antmicro/jetson-orin-baseboard/assets/wireframe/wireframe_dimensions.png

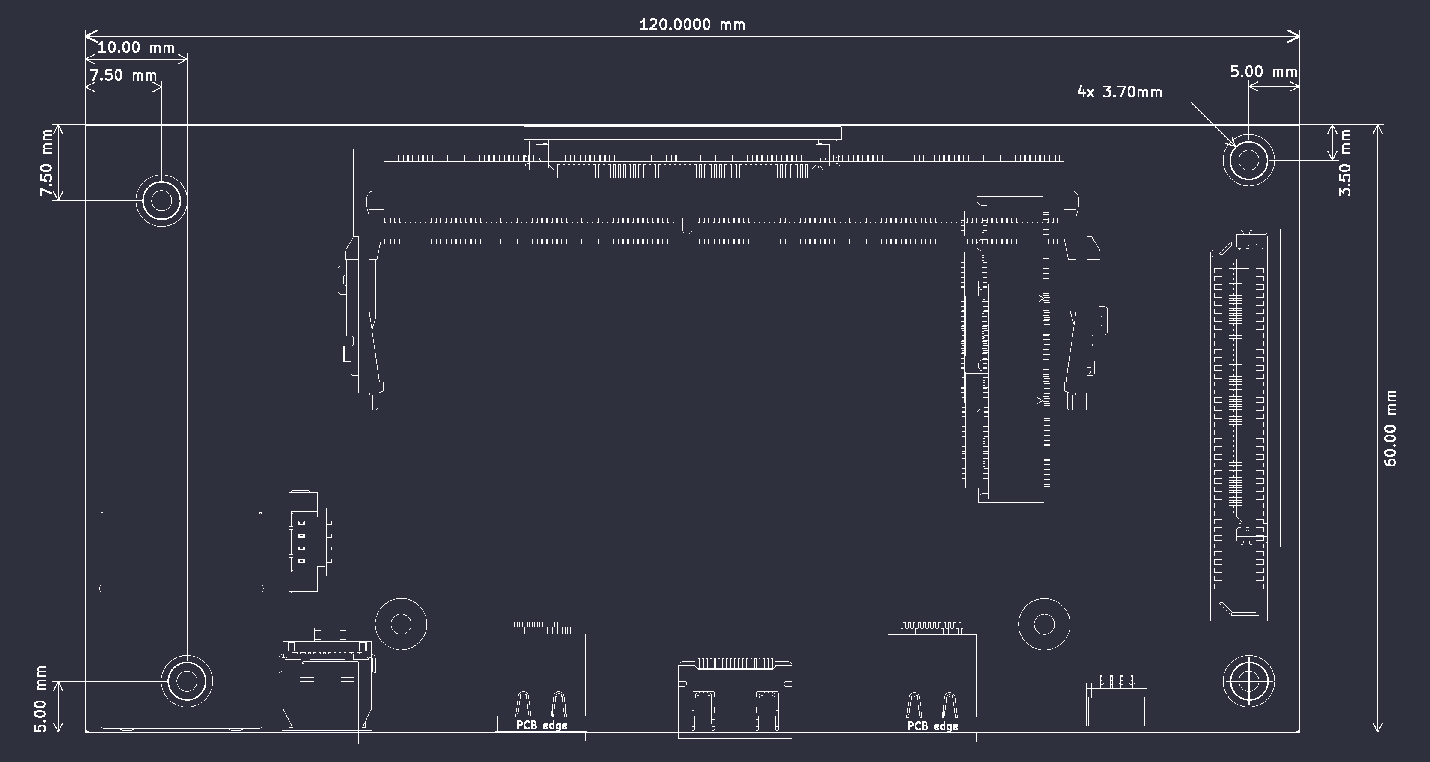
assets/wireframe/wireframe_dimensions.png
