antmicro/jetson-orin-baseboard/assets/wireframe/wireframe_dimensions_bottom.png

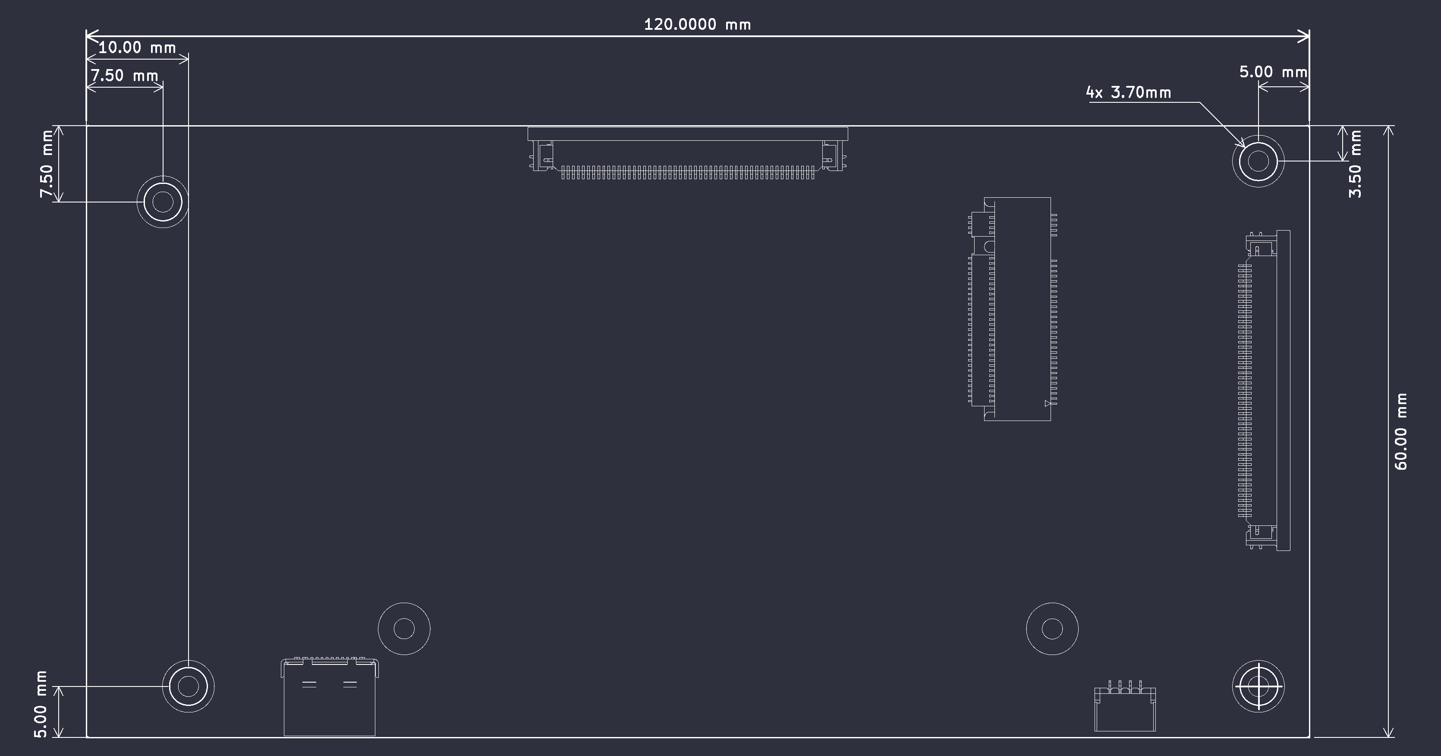
assets/wireframe/wireframe_dimensions_bottom.png
