antmicro/jetson-orin-baseboard/assets/wireframe/wireframe_dimensions_top.png

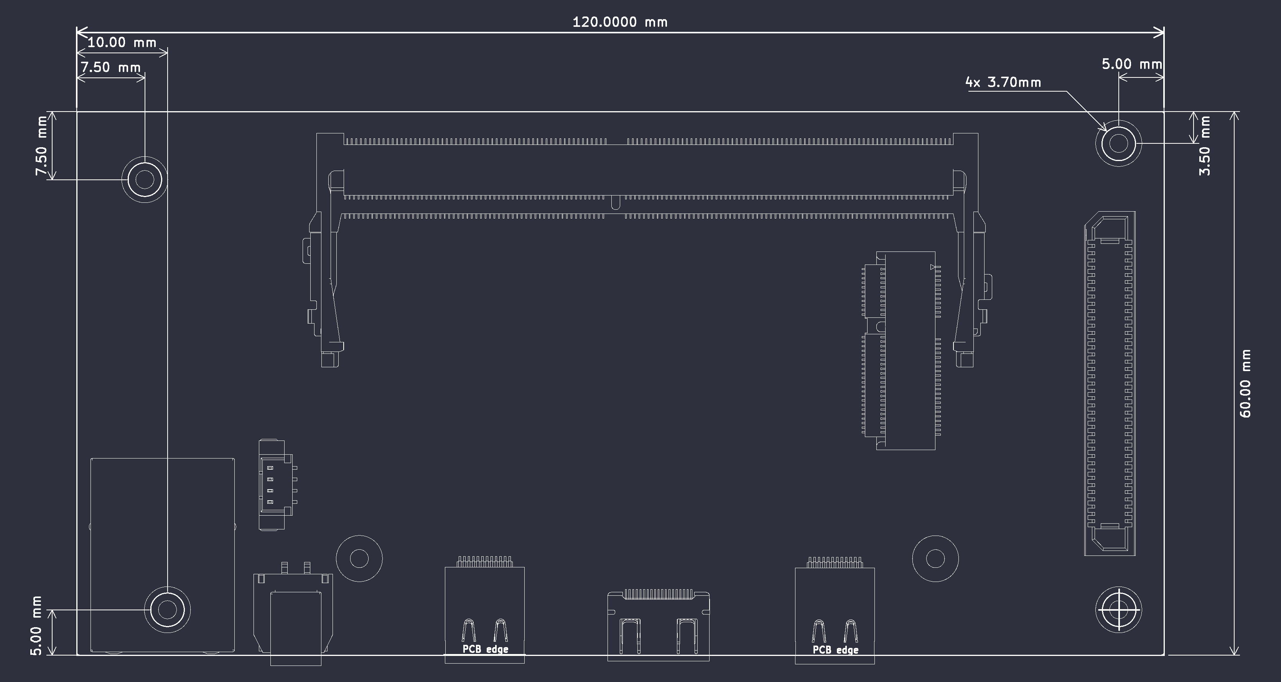
assets/wireframe/wireframe_dimensions_top.png
