antmicro/jetson-orin-baseboard/doc/source/img/3V3_eff_temp_vs_output_curr.png

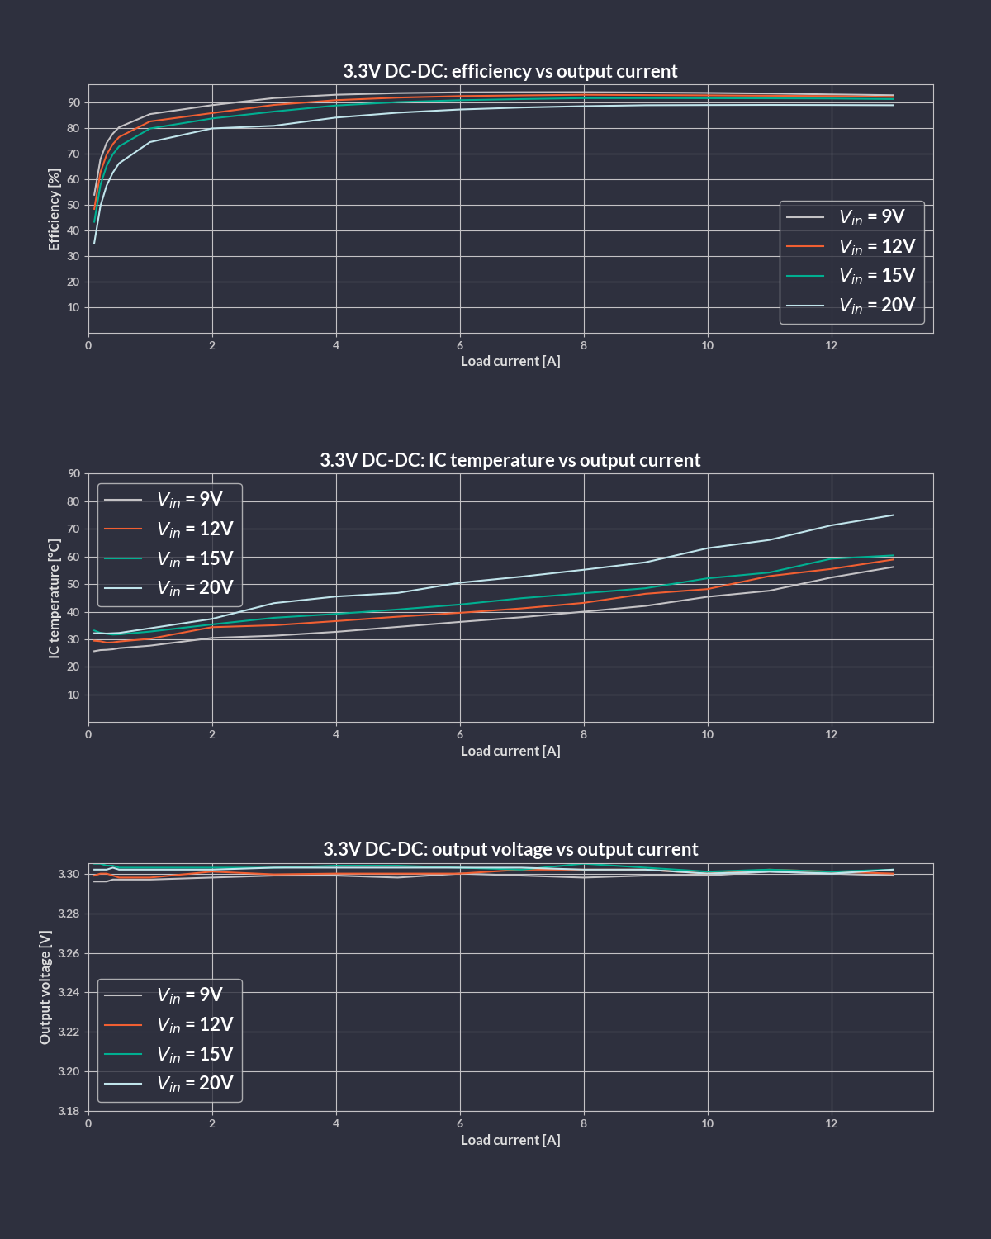
doc/source/img/3V3_eff_temp_vs_output_curr.png
